hanvith6/iot-network-monitoring-system/pcb/rtdms_v2.kicad_sch

## KiCad design pcb/rtdms_v2.kicad_sch (2026-04-03)

Schematic: rtdms_v2.kicad_sch

Parts:
C1, C3: 100nF; C_0805_2012Metric
C2: 10uF; C_0805_2012Metric
C4: 100uF; C_0805_2012Metric
J1: HC-SR04; PinHeader_1x04_P2.54mm_Vertical
J2: YF-S201; PinHeader_1x03_P2.54mm_Vertical
J3: SEN0189-Turbidity; PinHeader_1x03_P2.54mm_Vertical
J4: TDS-Meter-V1.0; PinHeader_1x03_P2.54mm_Vertical
J5: LCD1602-I2C; PinHeader_1x04_P2.54mm_Vertical
J_PWR: PWR-IN-5V; PinHeader_1x02_P2.54mm_Vertical
J_RAIL: PWR-RAIL; PinHeader_1x12_P2.54mm_Vertical
R_ECHO1: 1k; R_0805_2012Metric
R_ECHO2: 2k; R_0805_2012Metric
R_SCL: 4.7k; R_0805_2012Metric
R_SDA: 4.7k; R_0805_2012Metric
U1: ESP32-WROOM-32D; ESP32-WROOM-32
U2: AMS1117-3.3; SOT-223-3_TabPin2
